sp3ct3r1/control-de-acceso/Control de acceso/Control de acceso.kicad_sch

## KiCad design Control de acceso/Control de acceso.kicad_sch (2024-08-13)

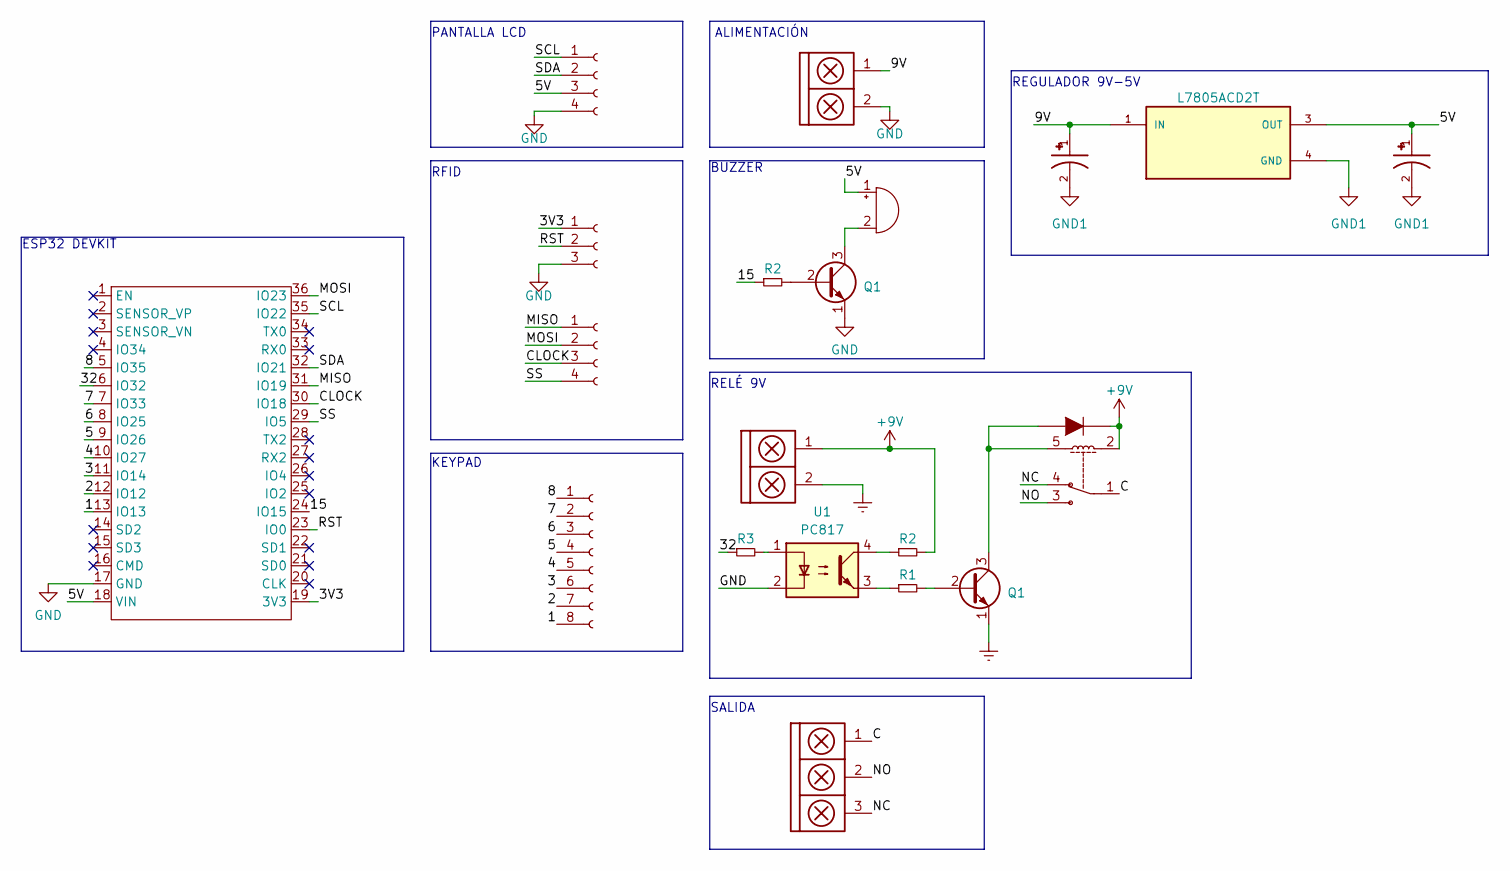
[picture p20: schematic Control de acceso.kicad_sch]

Parts:
BZ1: Buzzer; Buzzer_12x9.5RM7.6
C1, C2: EEEFC1H101P; CAP_EEEFC1H101P; PARTREV 10-Oct-19
D1: DIODE; D_SMA
J1: Conn_01x04_Socket; PinHeader_1x04_P2.54mm_Vertical
J2: Conn_01x08_Socket; PinHeader_1x08_P2.54mm_Vertical
J4: TBR; BORNERA2_AZUL
J5: TB; BORNERA2_AZUL
J6: TB_1X3; BORNERA3_Vertical
J7: Conn_01x03_Socket; PinHeader_1x03_P2.54mm_Vertical
K2: RELAY_C; Relay_C
Q1: 2N3904; SOT95P230X110-3N
R1, R2, R3: R; R_0805
U1: PC817; DIP-4_W7.62mm
U2: ESP32_DevKit_V1_DOIT; ESP32_DEVKIT_V1_DOIT
U3: L7805ACD2T; VREG_L7805ACD2T; PARTREV 34

Connections:
1: J2.8, U2.13 (IO13)
2: J2.7, U2.12 (IO12)
3: J2.6, U2.11 (IO14)
3V3: J7.1, U2.19 (3V3)
4: J2.5, U2.10 (IO27)
5: J2.4, U2.9 (IO26)
5V: BZ1.1 (-), C2.1, J1.3, U2.18 (VIN), U3.3 (OUT)
6: J2.3, U2.8 (IO25)
7: J2.2, U2.7 (IO33)
8: J2.1, U2.5 (IO35)
9V: C1.1, J5.1, U3.1 (IN)
15: R2.1, U2.24 (IO15)
32: R3.1, U2.6 (IO32)
+9V: D1.2 (K), J4.1, K2.2, R2.2
C: J6.1, K2.1
CLOCK: J1.3, U2.30 (IO18)
Earth: J4.2, Q1.1 (E)
GND: J1.4, J5.2, J7.3, Q1.1 (E), U1.2, U2.17 (GND)
GND1: C1.2, C2.2, U3.4 (GND)
MISO: J1.1, U2.31 (IO19)
MOSI: J1.2, U2.36 (IO23)
NC: J6.3, K2.4
NO: J6.2, K2.3
unnamed: BZ1.2 (+), Q1.3 (C)
unnamed: D1.1 (A), K2.5, Q1.3 (C)
unnamed: Q1.2 (B), R1.2, R2.2
unnamed: R1.1, U1.3
unnamed: R2.1, U1.4
unnamed: R3.2, U1.1
RST: J7.2, U2.23 (IO0)
SCL: J1.1, U2.35 (IO22)
SDA: J1.2, U2.32 (IO21)
SS: J1.4, U2.29 (IO5)

Notes on the sheet:
RELÉ 9V
BUZZER
KEYPAD
PANTALLA LCD
REGULADOR 9V-5V
ALIMENTACIÓN
RFID
SALIDA
ESP32 DEVKIT
